sparkfun/SparkFun_VR_IMU_Breakout_BNO086_QWIIC/docs/assets/img/22857-SEN_SparkFun_VR_IMU_Breakout-BNO086_Qwiic- 06.jpg

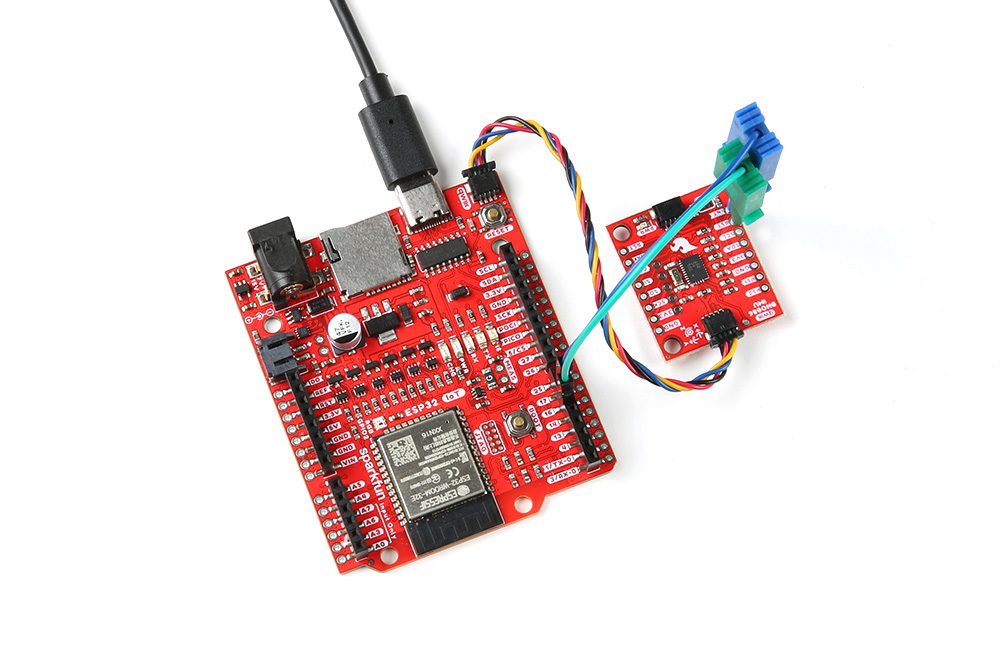
docs/assets/img/22857-SEN_SparkFun_VR_IMU_Breakout-BNO086_Qwiic- 06.jpg
